wirehead/gen3piano/gerber/gen3piano-F_SilkS.pdf

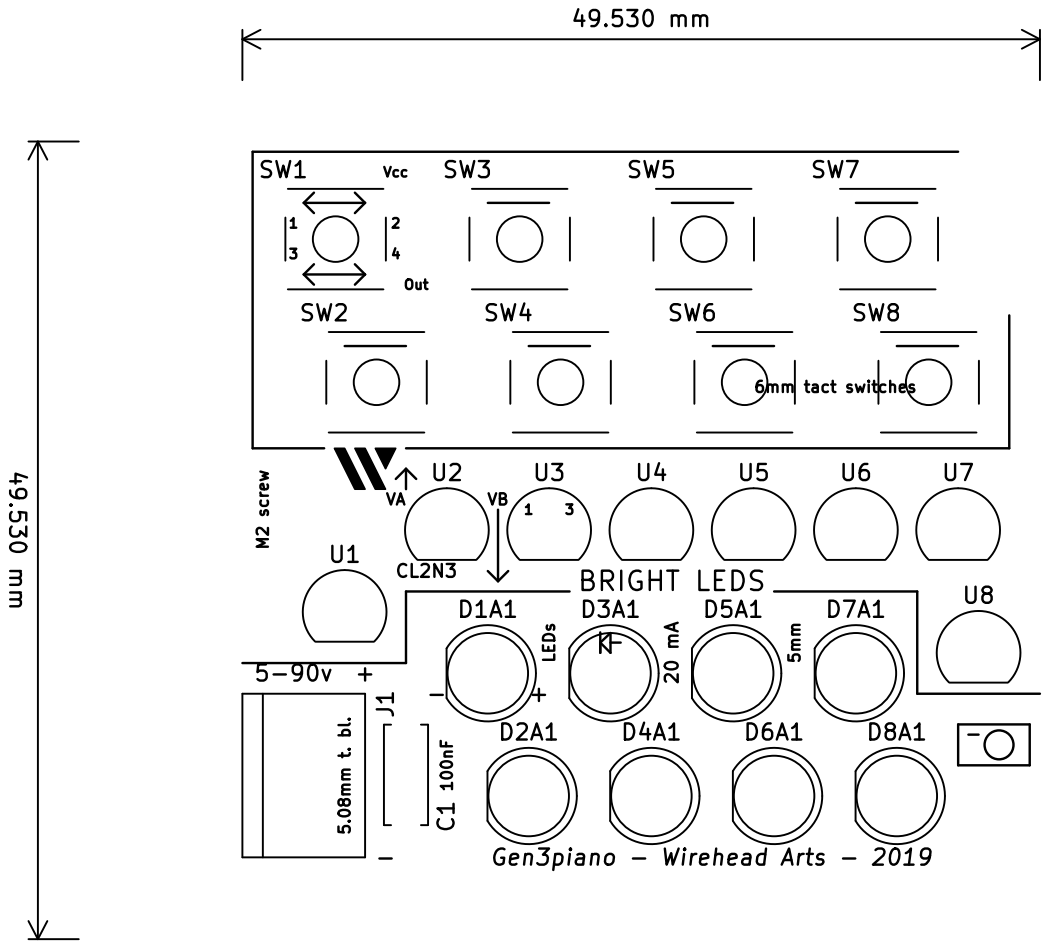
[picture p9: page 1]
